wagnerism/ender5plus-klipper-mercuryone/config/filament_sensor.cfg

# https://docs.vorondesign.com/community/howto/samwiseg0/btt_smart_filament_sensor.html
# https://github.com/bigtreetech/smart-filament-detection-module/blob/cfacc9a9630255bf735c1696e6a52b10a89cb8ba/readme.md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

[filament_motion_sensor SFS_T0]
detection_length: 10.00 ; This can be adjusted to your desired level of sensitivity. 10 is a recommended value to prevent flow dropoff false triggers.
extruder: extruder
switch_pin: ^PA4
pause_on_runout: True ; This can be set to false to debug false positives putting the sensor in "monitor mode". The printer will not pause but it will run the runout_gcode below.
event_delay: 3.0
pause_delay: 0.5
insert_gcode:
    M117 Insert Detected
runout_gcode:
    M117 Runout Detected

[delayed_gcode DISABLEFILAMENTSENSOR] ; This will disable the SFS 1 second after klipper starts
initial_duration: 1
gcode:
    SET_FILAMENT_SENSOR SENSOR=SFS_T0 ENABLE=0 ; Put your filament sensor's name after SENSOR=

[gcode_macro SFS_ENABLE] ; Add this to PRINT_START
description: Enable smart filament sensor
gcode:
    M117 ENABLING the Smart Filament Sensor
    G92 E0
    SET_FILAMENT_SENSOR SENSOR=SFS_T0 ENABLE=1 ; Put your filament sensor's name after SENSOR=

[gcode_macro SFS_DISABLE] ; Add this to PRINT_END and PRINT_CANCEL
description: Disable smart filament sensor
gcode:
    M117 DISABLING the Smart Filament Sensor
    G92 E0
    SET_FILAMENT_SENSOR SENSOR=SFS_T0 ENABLE=0 ; Put your filament sensor's name after SENSOR=

# https://ellis3dp.com/Print-Tuning-Guide/articles/index_useful_macros.html
[gcode_macro M109]
rename_existing: M99109
gcode:
    #Parameters
    {% set s = params.S|float %}
    
    M104 {% for p in params %}{'%s%s' % (p, params[p])}{% endfor %}  ; Set hotend temp
    {% if s != 0 %}
        TEMPERATURE_WAIT SENSOR=extruder MINIMUM={s} MAXIMUM={s+1}   ; Wait for hotend temp (within 1 degree)
    {% endif %}
